sammcj/screen-hopper/firmware/src/tinyusb_stuff.cc

/*
 * The MIT License (MIT)
 *
 * Copyright (c) 2022 Jacek Fedorynski
 * Copyright (c) 2019 Ha Thach (tinyusb.org)
 *
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
 */

#include <tusb.h>

#include "our_descriptor.h"

// These IDs are bogus. If you want to distribute any hardware using this,
// you will have to get real ones.
#define USB_VID 0xCAFE
#define USB_PID 0xBAF3

tusb_desc_device_t const desc_device = {
    .bLength = sizeof(tusb_desc_device_t),
    .bDescriptorType = TUSB_DESC_DEVICE,
    .bcdUSB = 0x0200,
    .bDeviceClass = 0x00,
    .bDeviceSubClass = 0x00,
    .bDeviceProtocol = 0x00,
    .bMaxPacketSize0 = CFG_TUD_ENDPOINT0_SIZE,

    .idVendor = USB_VID,
    .idProduct = USB_PID,
    .bcdDevice = 0x0100,

    .iManufacturer = 0x01,
    .iProduct = 0x02,
    .iSerialNumber = 0x00,

    .bNumConfigurations = 0x01,
};

#define CONFIG_TOTAL_LEN (TUD_CONFIG_DESC_LEN + TUD_HID_DESC_LEN)
#define EPNUM_HID 0x81

uint8_t const desc_configuration[] = {
    // Config number, interface count, string index, total length, attribute, power in mA
    TUD_CONFIG_DESCRIPTOR(1, 1, 0, CONFIG_TOTAL_LEN, TUSB_DESC_CONFIG_ATT_REMOTE_WAKEUP, 100),

    // Interface number, string index, protocol, report descriptor len, EP In address, size & polling interval
    TUD_HID_DESCRIPTOR(0, 0, HID_ITF_PROTOCOL_NONE, our_report_descriptor_length, EPNUM_HID, CFG_TUD_HID_EP_BUFSIZE, 1)
};

char const* string_desc_arr[] = {
    (const char[]){ 0x09, 0x04 },  // 0: is supported language is English (0x0409)
#ifdef IS_FORWARDER
    "Generic",                     // 1: Manufacturer
    "USB Keyboard/Mouse",          // 2: Product
#else
    "RP2040",                      // 1: Manufacturer
    "Screen Hopper",               // 2: Product
#endif
};

// Invoked when received GET DEVICE DESCRIPTOR
// Application return pointer to descriptor
uint8_t const* tud_descriptor_device_cb() {
    return (uint8_t const*) &desc_device;
}

// Invoked when received GET CONFIGURATION DESCRIPTOR
// Application return pointer to descriptor
// Descriptor contents must exist long enough for transfer to complete
uint8_t const* tud_descriptor_configuration_cb(uint8_t index) {
    return desc_configuration;
}

// Invoked when received GET HID REPORT DESCRIPTOR
// Application return pointer to descriptor
// Descriptor contents must exist long enough for transfer to complete
uint8_t const* tud_hid_descriptor_report_cb(uint8_t itf) {
    return our_report_descriptor;
}

static uint16_t _desc_str[32];

// Invoked when received GET STRING DESCRIPTOR request
// Application return pointer to descriptor, whose contents must exist long enough for transfer to complete
uint16_t const* tud_descriptor_string_cb(uint8_t index, uint16_t langid) {
    uint8_t chr_count;

    if (index == 0) {
        memcpy(&_desc_str[1], string_desc_arr[0], 2);
        chr_count = 1;
    } else {
        // Note: the 0xEE index string is a Microsoft OS 1.0 Descriptors.
        // https://docs.microsoft.com/en-us/windows-hardware/drivers/usbcon/microsoft-defined-usb-descriptors

        if (!(index < sizeof(string_desc_arr) / sizeof(string_desc_arr[0])))
            return NULL;

        const char* str = string_desc_arr[index];

        // Cap at max char
        chr_count = strlen(str);
        if (chr_count > 31)
            chr_count = 31;

        // Convert ASCII string into UTF-16
        for (uint8_t i = 0; i < chr_count; i++) {
            _desc_str[1 + i] = str[i];
        }
    }

    // first byte is length (including header), second byte is string type
    _desc_str[0] = (TUSB_DESC_STRING << 8) | (2 * chr_count + 2);

    return _desc_str;
}
